karlspace/Teo-der-Topf/Application/assets/emoji-animation/symbols/exclamation-double.gif

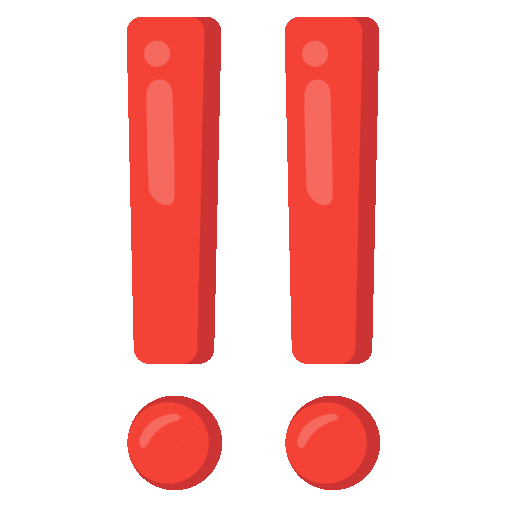
Application/assets/emoji-animation/symbols/exclamation-double.gif
